wyu31/TECHIN-514-FinalProject/Client_Code/include/Bass_Drum_data.h

#ifndef BASS_DRUM_DATA_H
#define BASS_DRUM_DATA_H

#include <cstdint>

const uint16_t bassDrumData[] = {
1984, 1984, 1982, 1982, 1982, 1982, 1981, 1981, 1980, 1980, 1979, 1979, 1978, 1978, 1977, 1977, 1977, 1977, 1976, 1976, 1975, 1975, 1974, 1974, 1973, 1973, 1972, 1972, 1972, 1972, 1971, 1971, 1970, 1970, 1970, 1970, 1969, 1969, 1968, 1968, 1967, 1967, 1966, 1966, 1965, 1965, 1965, 1965, 1965, 1965, 1964, 1964, 1964, 1964, 1963, 1963, 1962, 1962, 1960, 1960, 1960, 1960, 1959, 1959, 1958, 1958, 1958, 1958, 1957, 1957, 1957, 1957, 1956, 1956, 1955, 1955, 1955, 1955, 1954, 1954, 1954, 1954, 1954, 1954, 1954, 1954, 1953, 1953, 1952, 1952, 1952, 1952, 1951, 1951, 1950, 1950, 1949, 1949, 1949, 1949, 1948, 1948, 1948, 1948, 1948, 1948, 1948, 1948, 1947, 1947, 1947, 1947, 1947, 1947, 1947, 1947, 1947, 1947, 1947, 1947, 1947, 1947, 1947, 1947, 1947, 1947, 1947, 1947, 1946, 1946, 1946, 1946, 1946, 1946, 1946, 1946, 1945, 1945, 1944, 1944, 1944, 1944, 1944, 1944, 1944, 1944, 1944, 1944, 1944, 1944, 1944, 1944, 1944, 1944, 1944, 1944, 1944, 1944, 1944, 1944, 1945, 1945, 1945, 1945, 1944, 1944, 1944, 1944, 1945, 1945, 1945, 1945, 1945, 1945, 1945, 1945, 1945, 1945, 1945, 1945, 1946, 1946, 1946, 1946, 1947, 1947, 1946, 1946, 1946, 1946, 1947, 1947, 1947, 1947, 1947, 1947, 1947, 1947, 1947, 1947, 1948, 1948, 1948, 1948, 1949, 1949, 1949, 1949, 1950, 1950, 1950, 1950, 1950, 1950, 1951, 1951, 1951, 1951, 1952, 1952, 1952, 1952, 1953, 1953, 1953, 1953, 1953, 1953, 1953, 1953, 1954, 1954, 1954, 1954, 1954, 1954, 1955, 1955, 1956, 1956, 1957, 1957, 1957, 1957, 1958, 1958, 1958, 1958, 1958, 1958, 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
