wyu31/TECHIN-514-FinalProject/Client_Code/include/Crash_Cymbal_data.h

#ifndef CRASH_CYMBAL_DATA_H
#define CRASH_CYMBAL_DATA_H

#include <cstdint>

const uint16_t crashCymbalData[] = {
2047, 2047, 2047, 2047, 2047, 2047, 2047, 2047, 2047, 2047, 2047, 2047, 2047, 2047, 2047, 2047, 2047, 2047, 2047, 2047, 2047, 2047, 2047, 2047, 2047, 2047, 2047, 2047, 2047, 2047, 2047, 2047, 2047, 2047, 2047, 2047, 2047, 2047, 2047, 2047, 2047, 2047, 2047, 2047, 2047, 2047, 2047, 2047, 2047, 2047, 2047, 2047, 2047, 2047, 2047, 2047, 2047, 2047, 2047, 2047, 2047, 2047, 2047, 2047, 2047, 2047, 2047, 2047, 2047, 2047, 2047, 2047, 2047, 2047, 2047, 2047, 2047, 2047, 2047, 2047, 2047, 2047, 2047, 2047, 2047, 2047, 2047, 2047, 2047, 2047, 2065, 2065, 2065, 2065, 2065, 2065, 2063, 2063, 2060, 2060, 2057, 2057, 2059, 2059, 2062, 2062, 2063, 2063, 2062, 2062, 2061, 2061, 2061, 2061, 2059, 2059, 2055, 2055, 2054, 2054, 2056, 2056, 2057, 2057, 2055, 2055, 2053, 2053, 2053, 2053, 2052, 2052, 2053, 2053, 2053, 2053, 2052, 2052, 2051, 2051, 2052, 2052, 2052, 2052, 2049, 2049, 2046, 2046, 2047, 2047, 2048, 2048, 2048, 2048, 2047, 2047, 2048, 2048, 2049, 2049, 2046, 2046, 2043, 2043, 2042, 2042, 2044, 2044, 2044, 2044, 2042, 2042, 2042, 2042, 2043, 2043, 2043, 2043, 2031, 2031, 2030, 2030, 2035, 2035, 2038, 2038, 2032, 2032, 2030, 2030, 2037, 2037, 2040, 2040, 2034, 2034, 2031, 2031, 2035, 2035, 2035, 2035, 2028, 2028, 2025, 2025, 2028, 2028, 2027, 2027, 2020, 2020, 2016, 2016, 2014, 2014, 2010, 2010, 2009, 2009, 2009, 2009, 2006, 2006, 2002, 2002, 2004, 2004, 2007, 2007, 2007, 2007, 2006, 2006, 2006, 2006, 2002, 2002, 2000, 2000, 2001, 2001, 2002, 2002, 2001, 2001, 2004, 2004, 2007, 2007, 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
