wyu31/TECHIN-514-FinalProject/Client_Code/include/Hi_Hat_data.h

#ifndef HI_HAT_DATA_H
#define HI_HAT_DATA_H

#include <cstdint>

const uint16_t hiHatData[] = {
2047, 2047, 2047, 2047, 2047, 2047, 2047, 2047, 2047, 2047, 2047, 2047, 2047, 2047, 2047, 2047, 2047, 2047, 2047, 2047, 2047, 2047, 2047, 2047, 2047, 2047, 2047, 2047, 2047, 2047, 2047, 2047, 2047, 2047, 2047, 2047, 2047, 2047, 2047, 2047, 2047, 2047, 2047, 2047, 2047, 2047, 2047, 2047, 2047, 2047, 2047, 2047, 2047, 2047, 2047, 2047, 2047, 2047, 2047, 2047, 2047, 2047, 2047, 2047, 2047, 2047, 2047, 2047, 2047, 2047, 2047, 2047, 2047, 2047, 2047, 2047, 2047, 2047, 2047, 2047, 2047, 2047, 2047, 2047, 2047, 2047, 2047, 2047, 2047, 2047, 2015, 2015, 2049, 2049, 2045, 2045, 2027, 2027, 2044, 2044, 2027, 2027, 2032, 2032, 2167, 2167, 2226, 2226, 2015, 2015, 1838, 1838, 1975, 1975, 2133, 2133, 2062, 2062, 2027, 2027, 2159, 2159, 2163, 2163, 2014, 2014, 2045, 2045, 2222, 2222, 2214, 2214, 2068, 2068, 2025, 2025, 1988, 1988, 1843, 1843, 1835, 1835, 2053, 2053, 2156, 2156, 2034, 2034, 2027, 2027, 2211, 2211, 2241, 2241, 2073, 2073, 2032, 2032, 2130, 2130, 2101, 2101, 1984, 1984, 1976, 1976, 2001, 2001, 1957, 1957, 1971, 1971, 2049, 2049, 2035, 2035, 1999, 1999, 2163, 2163, 2391, 2391, 2298, 2298, 2103, 2103, 1997, 1997, 1838, 1838, 1724, 1724, 1886, 1886, 2123, 2123, 2164, 2164, 2094, 2094, 1997, 1997, 1888, 1888, 1955, 1955, 2173, 2173, 2178, 2178, 2023, 2023, 2092, 2092, 2217, 2217, 2056, 2056, 1951, 1951, 2220, 2220, 2412, 2412, 2213, 2213, 2007, 2007, 2044, 2044, 2131, 2131, 2165, 2165, 2076, 2076, 1757, 1757, 1519, 1519, 1767, 1767, 2194, 2194, 2269, 2269, 2094, 2094, 1978, 1978, 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
