wyu31/TECHIN-514-FinalProject/Client_Code/include/Snare_Drum_data.h

#ifndef SNARE_DRUM_DATA_H
#define SNARE_DRUM_DATA_H

#include <cstdint>

const uint16_t snareDrumData[] = {
2047, 2047, 2047, 2047, 2047, 2047, 2047, 2047, 2047, 2047, 2047, 2047, 2047, 2047, 2047, 2047, 2047, 2047, 2047, 2047, 2047, 2047, 2047, 2047, 2047, 2047, 2047, 2047, 2047, 2047, 2047, 2047, 2047, 2047, 2047, 2047, 2047, 2047, 2047, 2047, 2047, 2047, 2047, 2047, 2047, 2047, 2047, 2047, 2047, 2047, 2047, 2047, 2047, 2047, 2047, 2047, 2047, 2047, 2047, 2047, 2047, 2047, 2047, 2047, 2047, 2047, 2047, 2047, 2047, 2047, 2047, 2047, 2047, 2047, 2047, 2047, 2047, 2047, 2047, 2047, 2047, 2047, 2047, 2047, 2047, 2047, 2047, 2047, 2047, 2047, 2048, 2048, 2048, 2048, 2048, 2048, 2048, 2048, 2048, 2048, 2048, 2048, 2048, 2048, 2048, 2048, 2048, 2048, 2047, 2047, 2047, 2047, 2047, 2047, 2047, 2047, 2047, 2047, 2047, 2047, 2047, 2047, 2047, 2047, 2047, 2047, 2047, 2047, 2047, 2047, 2047, 2047, 2047, 2047, 2047, 2047, 2047, 2047, 2047, 2047, 2047, 2047, 2047, 2047, 2047, 2047, 2047, 2047, 2047, 2047, 2047, 2047, 2047, 2047, 2047, 2047, 2047, 2047, 2047, 2047, 2047, 2047, 2047, 2047, 2047, 2047, 2047, 2047, 2047, 2047, 2046, 2046, 2046, 2046, 2046, 2046, 2046, 2046, 2046, 2046, 2046, 2046, 2046, 2046, 2045, 2045, 2045, 2045, 2045, 2045, 2045, 2045, 2045, 2045, 2045, 2045, 2045, 2045, 2045, 2045, 2045, 2045, 2045, 2045, 2045, 2045, 2045, 2045, 2045, 2045, 2045, 2045, 2045, 2045, 2045, 2045, 2044, 2044, 2044, 2044, 2044, 2044, 2044, 2044, 2044, 2044, 2044, 2044, 2044, 2044, 2044, 2044, 2044, 2044, 2044, 2044, 2044, 2044, 2044, 2044, 2044, 2044, 2044, 2044, 2044, 2044, 2044, 2044, 2044, 2044, 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
